tanu-abburi/Digital-Stethoscope/simulation/esdp.asc

C1: cap; 100n
C2: cap; 100n
C3: cap; 10µ
C4: cap; 500p
C5: cap; 10µ
D1: diode
D2: diode
J1: njf
R1: res; 10k
R2: res; 6.67k
R3: res; 1Meg
R4: res; 20k
R5: res; 20k
R6: res; 1k
R7: res; 1k
R8: res; 2.2k
U1: OP07
V1: voltage; 5
V2: voltage; SINE(0 0.05 20)
Named nets: 0, vdd, out
.tran 0 500m 0
